zuidec/xbx-nrf/pcb/xbx-nrf/xbx-nrf.kicad_sch

## KiCad design pcb/xbx-nrf/xbx-nrf.kicad_sch (2026-09-29)

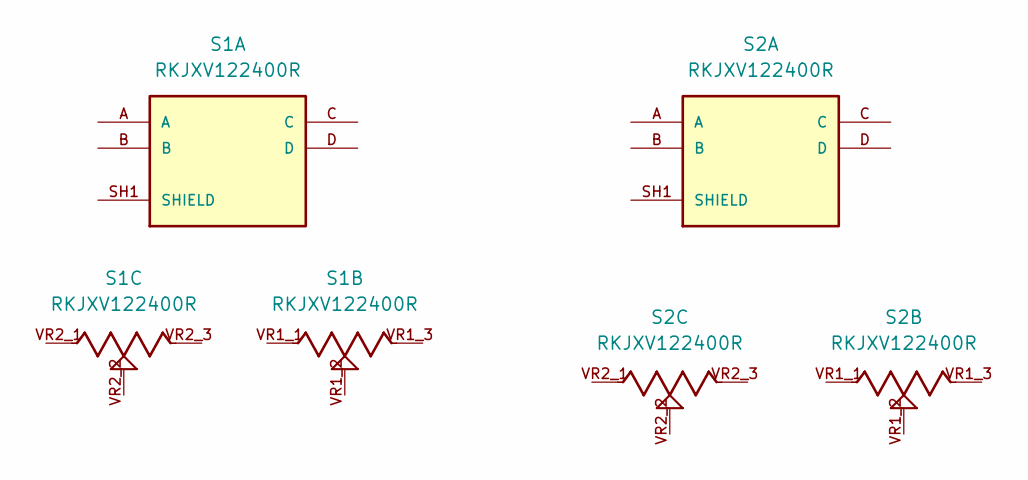
[picture p3: schematic xbx-nrf.kicad_sch]

Parts:
S1, S2: RKJXV122400R; SW_RKJXV122400R; PARTREV N/A

Connections:
unnamed: S1.SH1 (SHIELD), S1.SH2 (SHIELD), S1.SH3 (SHIELD), S1.SH4 (SHIELD)
unnamed: S2.SH1 (SHIELD), S2.SH2 (SHIELD), S2.SH3 (SHIELD), S2.SH4 (SHIELD)
